watterott/Robo-Badge/software/TV-Off/config.h

#include <avr/pgmspace.h>

// Lets us calculate the size of the NA/EU databases
#define NUM_ELEM(x) (sizeof (x) / sizeof (*(x)));

// set define to 0 to turn off debug output
#define DEBUG 0
#define DEBUGP(x) if (DEBUG == 1) { x ; }
#define putstring_nl(s) Serial.println(s)
#define putstring(s) Serial.print(s)
#define putnum_ud(n) Serial.print(n, DEC)
#define putnum_uh(n) Serial.print(n, HEX)

// Shortcut to insert single, non-optimized-out nop
#define NOP __asm__ __volatile__ ("nop")

// Tweak this if neccessary to change timing
// -for 8MHz Arduinos, a good starting value is 11
// -for 16MHz Arduinos, a good starting value is 25
#define DELAY_CNT 13 //11...14

// Makes the codes more readable. the OCRA is actually
// programmed in terms of 'periods' not 'freqs' - that
// is, the inverse!
#define freq_to_timerval(x) ((F_CPU / x - 1)/ 2)

// The structure of compressed code entries
struct IrCode {
  uint8_t timer_val;
  uint8_t numpairs;
  uint8_t bitcompression;
  uint16_t const *times;
  uint8_t const *codes;
};
